prparsons/AutoScale/stm/inc/DEV_Config.h

/*****************************************************************************
* | File      	:   DEV_Config.h
* | Author      :   Waveshare team
* | Function    :   Hardware underlying interface
* | Info        :
*                Used to shield the underlying layers of each master 
*                and enhance portability
*----------------
* |	This version:   V1.0
* | Date        :   2018-11-22
* | Info        :

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
******************************************************************************/
#ifndef _DEV_CONFIG_H_
#define _DEV_CONFIG_H_

//stm32f4xx_hal_conf
#include "stm32f4xx_hal.h"
#include <stdint.h>
#include <stdio.h>
#include "main.h"

#define UBYTE   uint8_t
#define UWORD   uint16_t
#define UDOUBLE uint32_t

SPI_HandleTypeDef* p_hspi_lcd;
TIM_HandleTypeDef* p_htim_lcd;

/**
 * GPIO config
**/
#define DEV_RST_PIN     RST_GPIO_Port,RST_Pin		//PA9
#define DEV_DC_PIN      DC_GPIO_Port,DC_Pin			//PA8
#define DEV_CS_PIN			CS_GPIO_Port,CS_Pin			//PB6
#define DEV_BL_PIN			TIM3->CCR2 							//PC7

/**
 * GPIO read and write
**/
#define DEV_Digital_Write(_pin, _value) HAL_GPIO_WritePin(_pin, _value == 0? GPIO_PIN_RESET:GPIO_PIN_SET)
#define DEV_Digital_Read(_pin) HAL_GPIO_ReadPin(_pin)

/**
 * SPI
**/
#define DEV_SPI_WRITE(_dat)  DEV_SPI_WRite(_dat);

/**
 * delay x ms
**/
#define DEV_Delay_ms(__xms) HAL_Delay(__xms)

/**
 * PWM_BL
**/

#define DEV_Set_PWM(_Value)     DEV_BL_PIN= _Value

/*-----------------------------------------------------------------------------*/
void DEV_SPI_WRite(UBYTE _dat);
int DEV_Module_Init(SPI_HandleTypeDef* hspi, TIM_HandleTypeDef* htim);
void DEV_Module_Exit(void);
#endif
